FGarridoV/BuBird/parts_3d/bird_house/files/dachblende.stl

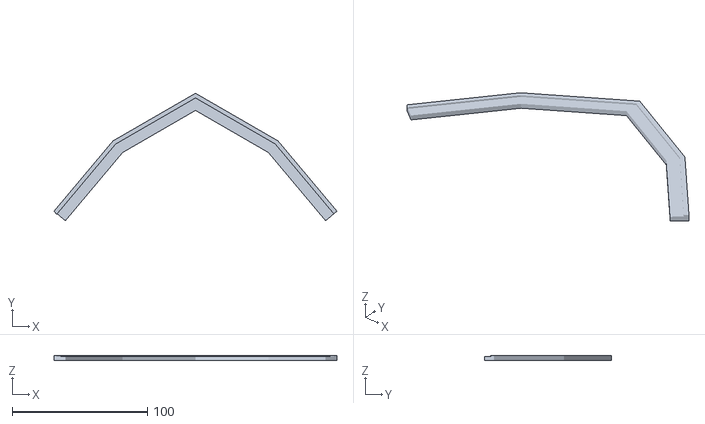
[picture p15: CAD file, 2026-03-07]
parts_3d/bird_house/files/dachblende.stl
209.4 x 94.3 x 4.00
