FGarridoV/BuBird/parts_3d/bird_house/files/fenster_klein.stl

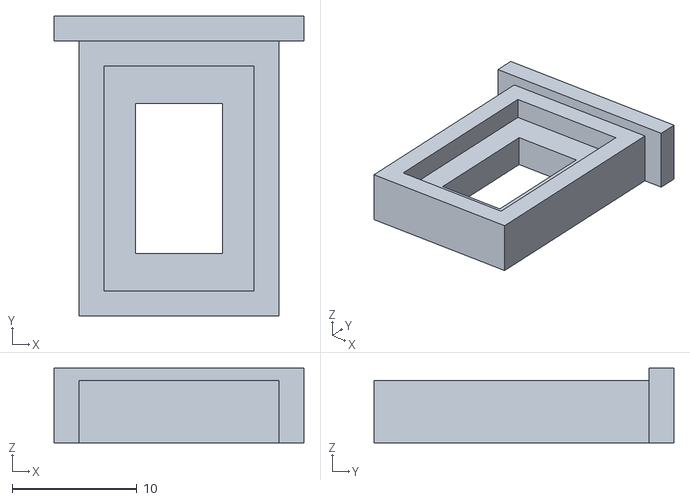
[picture p16: CAD file, 2026-03-07]
parts_3d/bird_house/files/fenster_klein.stl
20.0 x 24.0 x 6.00
