FGarridoV/BuBird/parts_3d/bird_house/files/fasssade_01.stl

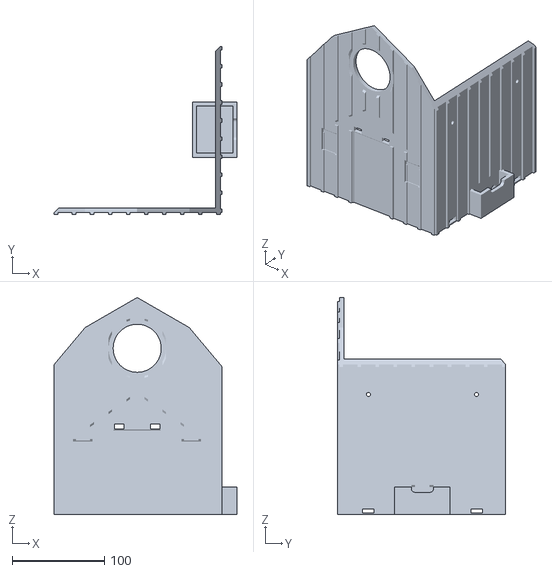
[picture p17: CAD file, 2026-03-07]
parts_3d/bird_house/files/fasssade_01.stl
198.0 x 182.0 x 235.0
