FGarridoV/BuBird/parts_3d/bird_house/files/montageleiste_2.stl

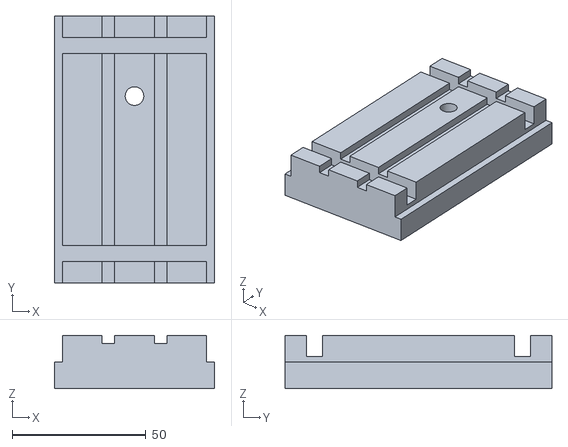
[picture p18: CAD file, 2026-03-07]
parts_3d/bird_house/files/montageleiste_2.stl
60.0 x 100.0 x 20.0
