FGarridoV/BuBird/parts_3d/bird_house/files/seitenwand_links.stl

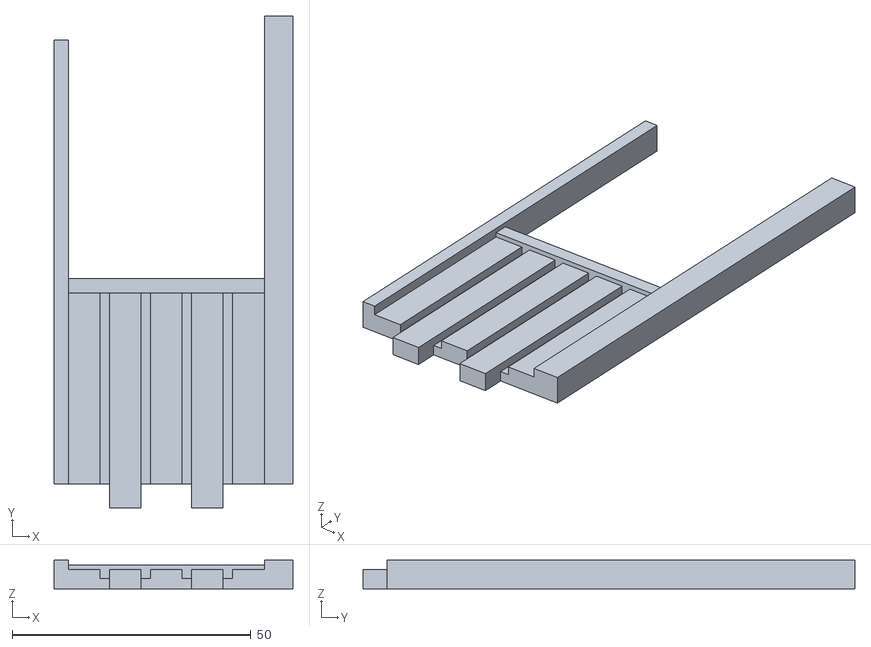
[picture p19: CAD file, 2026-03-07]
parts_3d/bird_house/files/seitenwand_links.stl
50.0 x 103.0 x 6.00
