FGarridoV/BuBird/parts_3d/bird_house/files/einflugring_mutter.stl

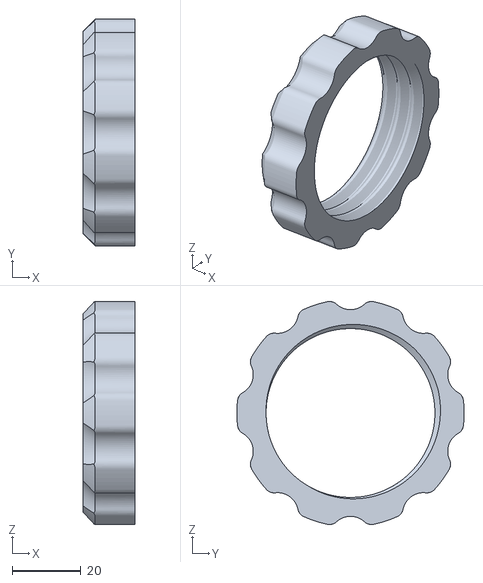
[picture p20: CAD file, 2026-03-07]
parts_3d/bird_house/files/einflugring_mutter.stl
15.0 x 66.0 x 64.7
