FGarridoV/BuBird/parts_3d/bird_house/files/dachrinne.stl

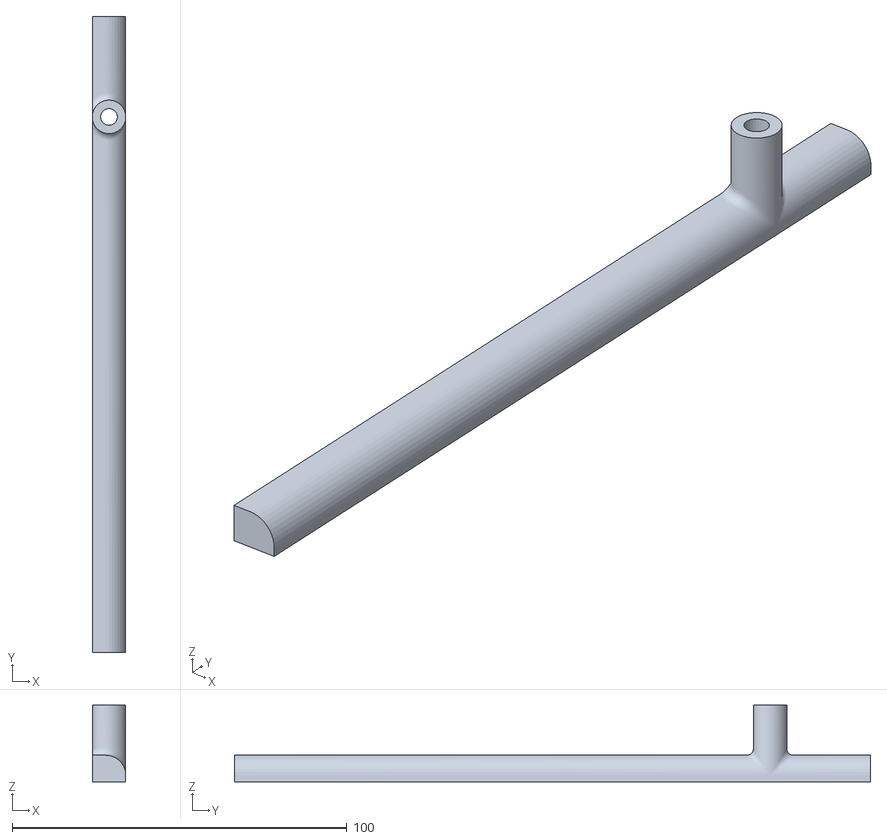
[picture p21: CAD file, 2026-03-07]
parts_3d/bird_house/files/dachrinne.stl
10.0 x 190.0 x 23.0
