FGarridoV/BuBird/parts_3d/bird_house/files/boden_v2.stl

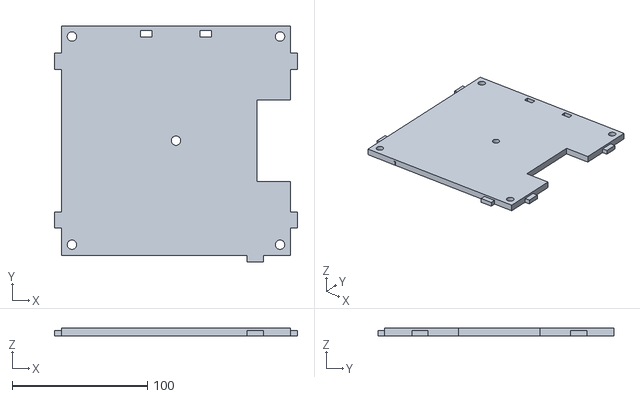
[picture p22: CAD file, 2026-03-07]
parts_3d/bird_house/files/boden_v2.stl
179.8 x 174.8 x 6.00
