FGarridoV/BuBird/parts_3d/bird_house/files/boden_v2_without_water_reservoir.stl

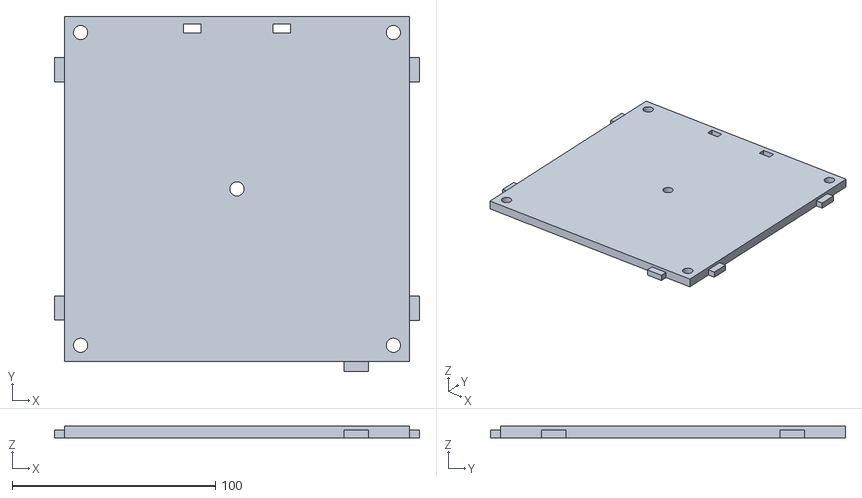
[picture p23: CAD file, 2026-03-07]
parts_3d/bird_house/files/boden_v2_without_water_reservoir.stl
179.8 x 174.8 x 6.00
