FGarridoV/BuBird/parts_3d/bird_house/files/einflugring_gewinde.stl

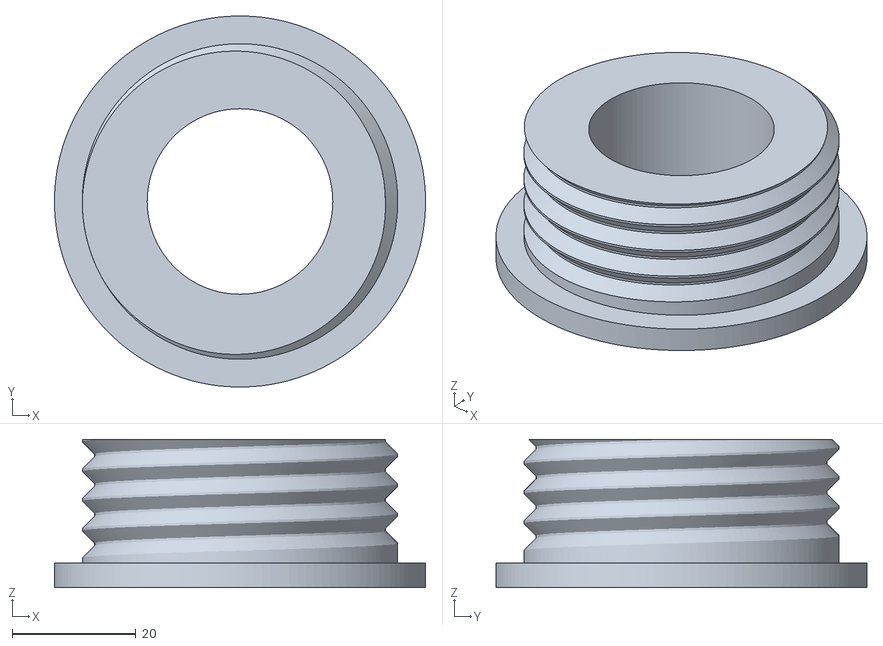
[picture p24: CAD file, 2026-03-07]
parts_3d/bird_house/files/einflugring_gewinde.stl
60.0 x 60.0 x 24.0
