FGarridoV/BuBird/parts_3d/bird_house/files/einflugring.stl

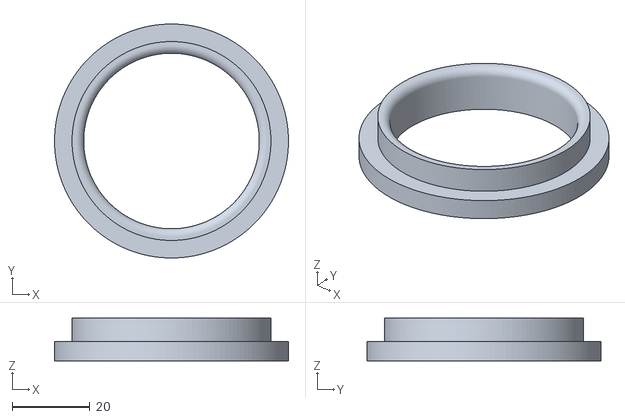
[picture p25: CAD file, 2026-03-07]
parts_3d/bird_house/files/einflugring.stl
60.0 x 60.0 x 11.0
