FGarridoV/BuBird/parts_3d/bird_house/files/montageleiste.stl

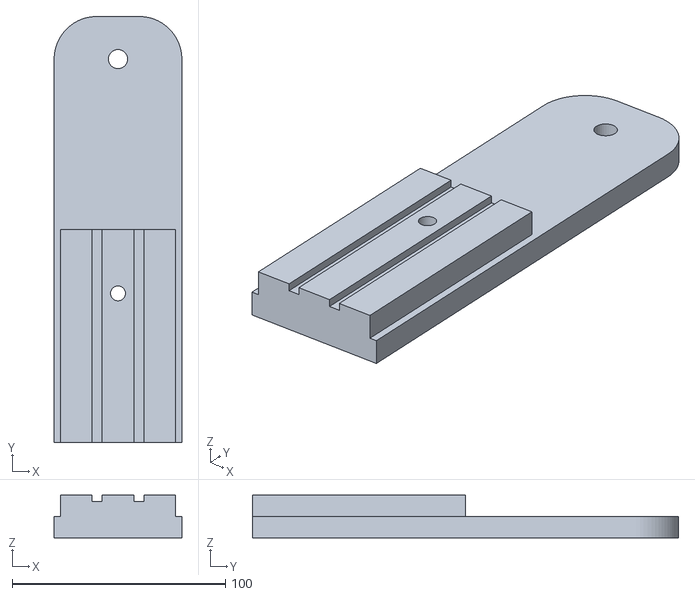
[picture p26: CAD file, 2026-03-07]
parts_3d/bird_house/files/montageleiste.stl
60.0 x 200.0 x 20.0
