FGarridoV/BuBird/parts_3d/bird_house/files/tuer.stl

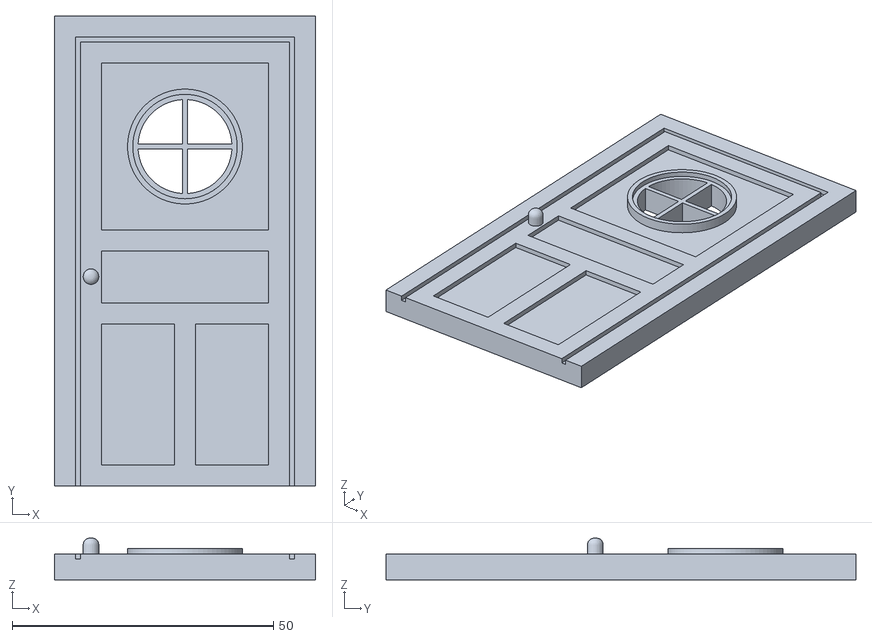
[picture p27: CAD file, 2026-03-07]
parts_3d/bird_house/files/tuer.stl
50.0 x 90.0 x 8.00
