FGarridoV/BuBird/parts_3d/bird_house/files/gehaeuse_v2_without_water_reservoir.stl

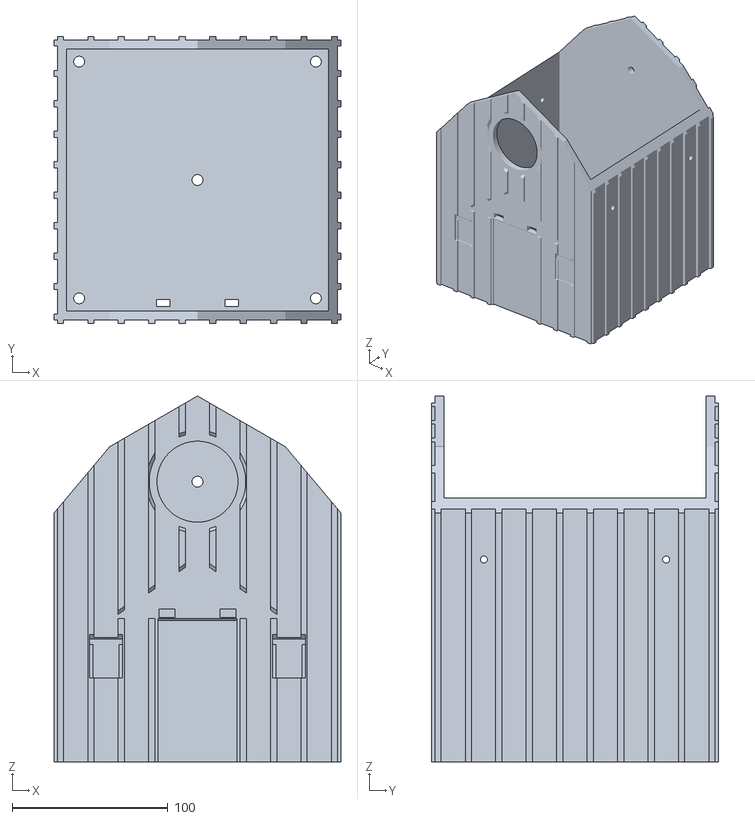
[picture p28: CAD file, 2026-03-07]
parts_3d/bird_house/files/gehaeuse_v2_without_water_reservoir.stl
184.0 x 184.0 x 235.0
